amearare54/arare/model/case/middle plate R 2.stl

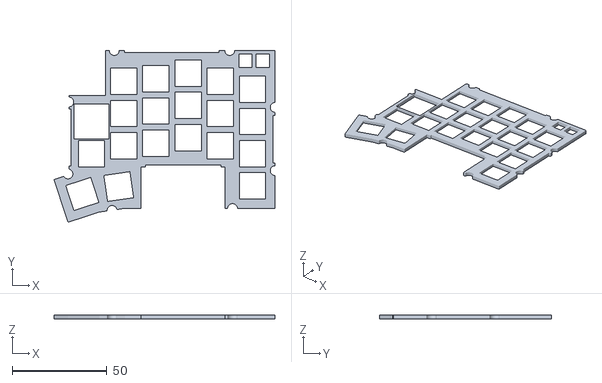
[picture p21: CAD file, 2026-09-01]
model/case/middle plate R 2.stl
116.6 x 90.5 x 2.20
