amearare54/arare/model/case/gasket mount L.stl

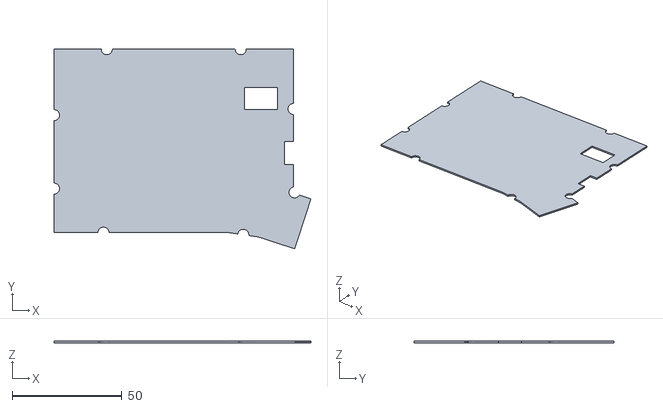
[picture p22: CAD file, 2026-09-01]
model/case/gasket mount L.stl
116.8 x 90.8 x 0.8
