amearare54/arare/model/case/horizontal rotary encoder 1.stl

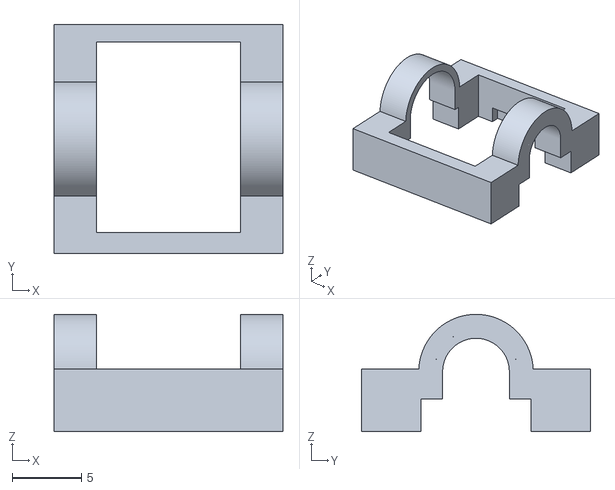
[picture p23: CAD file, 2026-09-01]
model/case/horizontal rotary encoder 1.stl
16.5 x 16.5 x 8.45
