amearare54/arare/model/case/middle plate L 1.stl

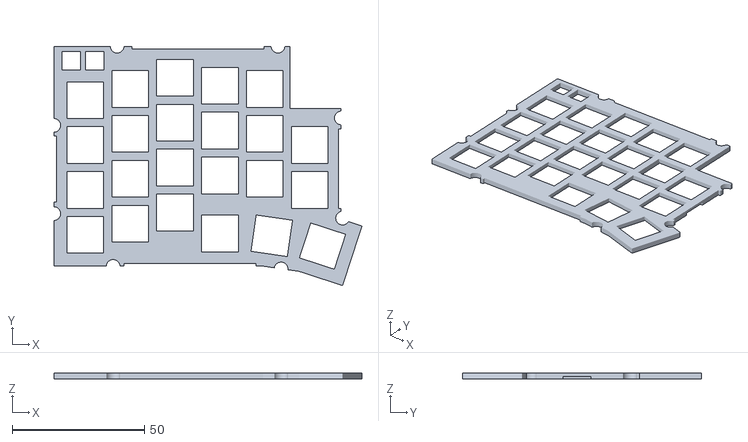
[picture p24: CAD file, 2026-09-01]
model/case/middle plate L 1.stl
116.6 x 90.5 x 2.20
